krishenmathur1000/Analog-DJ-Board/simulation/Deck A passive crossfader.asc

C1: cap; 0.1µ
C2: cap; 0.1µ
R1: res; {10k*(1-aA)}
R2: res; {10k*aA}
R3: res; {160 + 10k*bA}
R4: res; {10k*(1-aB)}
R5: res; {10k*aB}
R6: res; {160 + 10k*bB}
R7: res; {10k*x+1}
R8: res; {10k*(1-x)+1}
U1: UniversalOpAmp2
U2: UniversalOpAmp2
V1: voltage; 0; AC 1
V2: voltage; 12
V3: voltage; 12
V4: voltage; 0; AC 0
V5: voltage; 12
V6: voltage; 12
Named nets: 0, DECKA_VOL_OUT, DECKA_FILTER_OUT, DECKB_VOL_OUT, DECKB_FILTER_OUT, XFADE
.ac dec 100 20 20k
.param aA=0.5
.param aB=0.5
.param bA=0
.param bB=0
.step param x list 0 0.25 0.5 0.75 1
