krishenmathur1000/Analog-DJ-Board/simulation/Deck A passive.asc

C1: cap; 0.1µ
R1: res; {10k*(1-a)}
R2: res; {10k*a}
R3: res; {160 + 10k*b}
V1: voltage; 0; AC 1
Named nets: 0, VOL_OUT, FILTER_OUT
.ac dec 100 20 20k
.param a=0.5
.param b=1
.step param b list 0.1 0.25 0.5 0.75 1
