krishenmathur1000/Analog-DJ-Board/results/crossfader_step_response.png

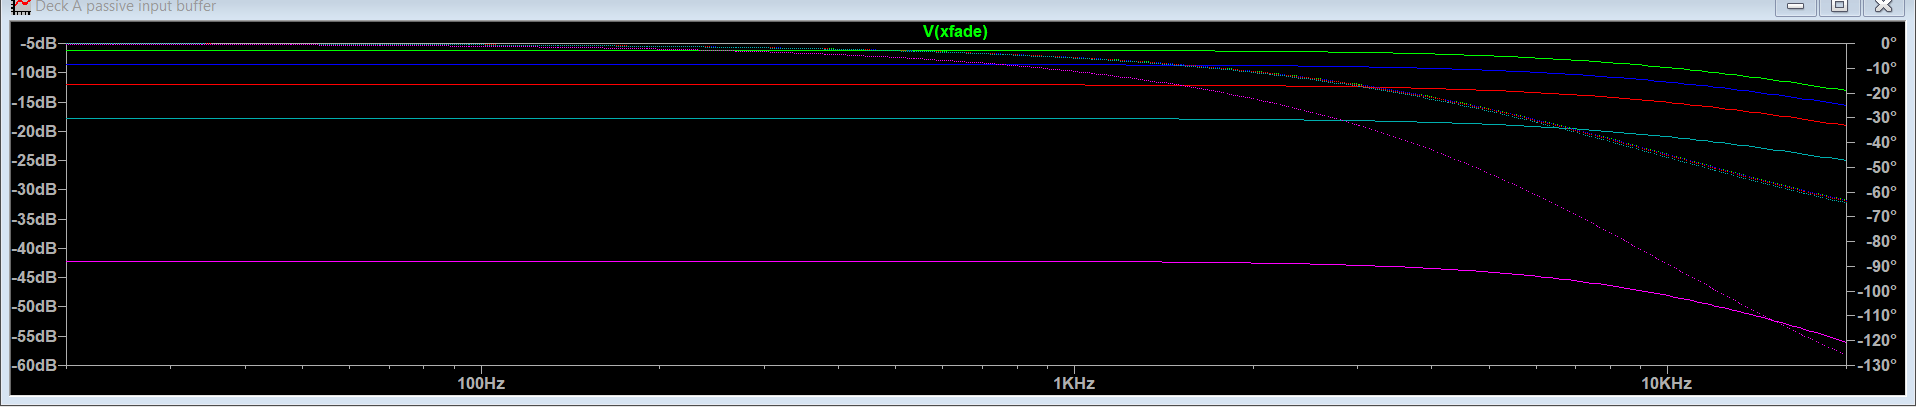
results/crossfader_step_response.png
