krishenmathur1000/Analog-DJ-Board/results/constant_power_plot.png

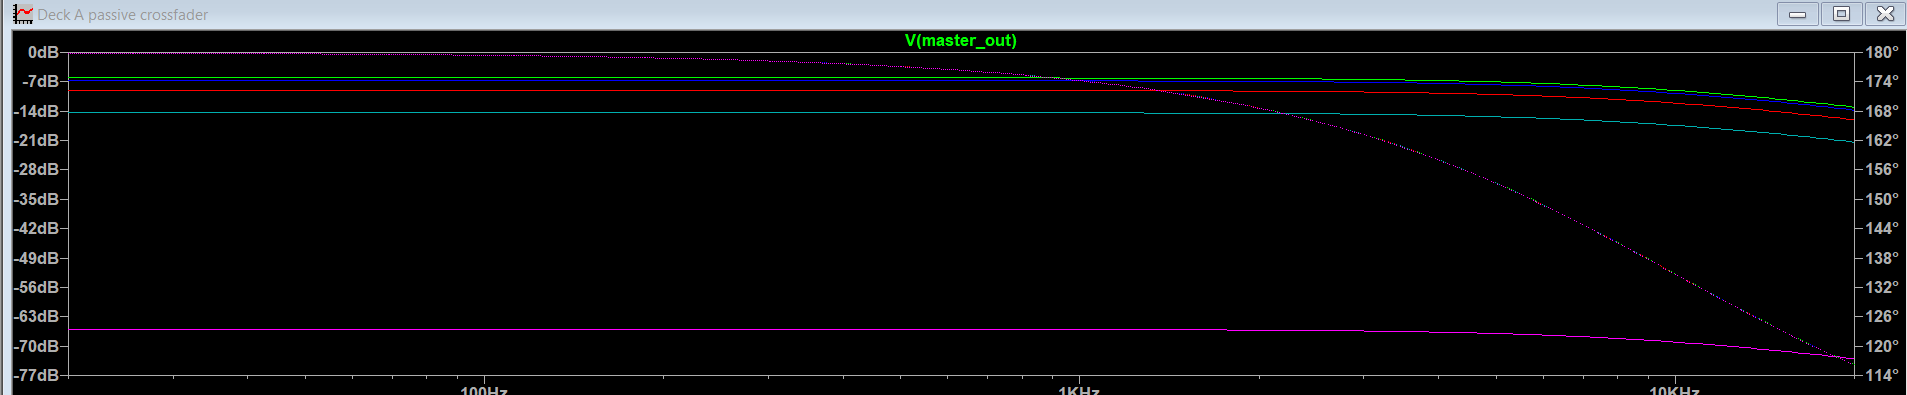
results/constant_power_plot.png
