krishenmathur1000/Analog-DJ-Board/results/Deck_A_passive.png

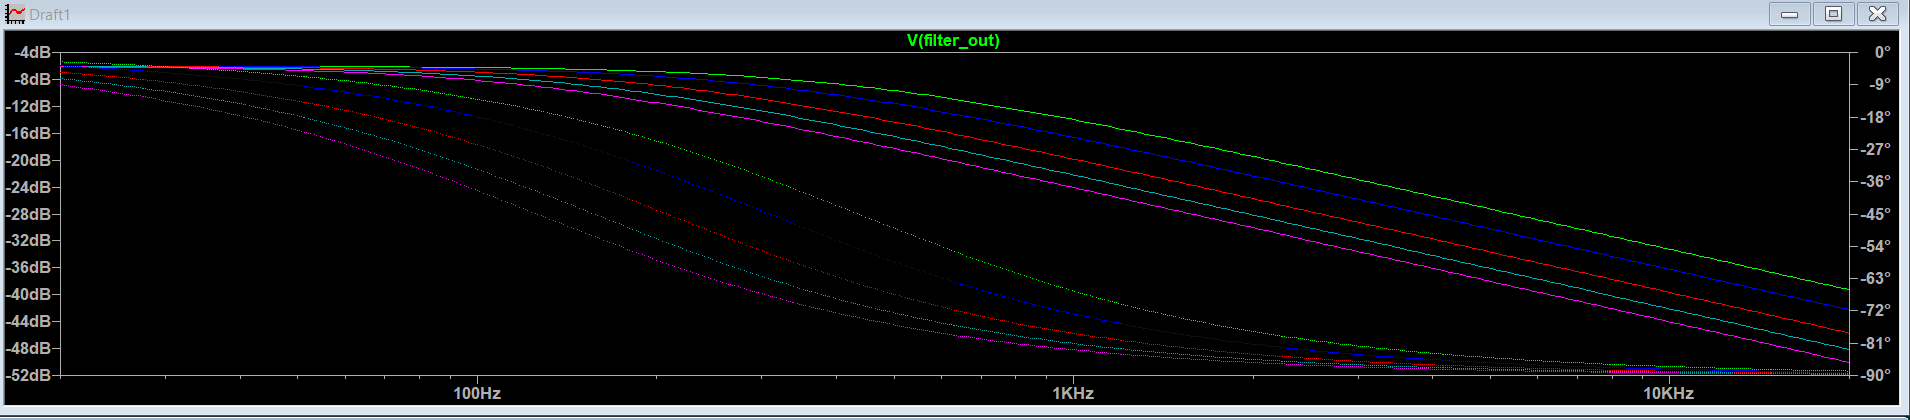
results/Deck_A_passive.png
