krishenmathur1000/Analog-DJ-Board/results/summing_amp.png

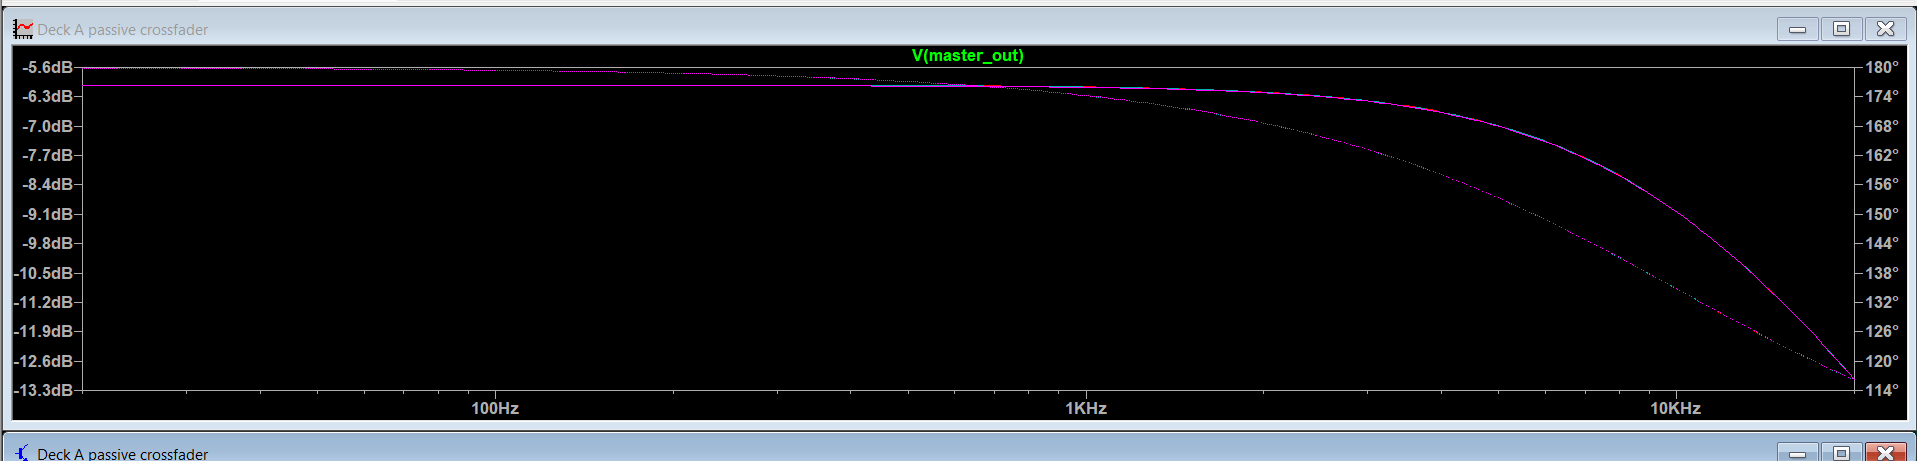
results/summing_amp.png
