krishenmathur1000/Analog-DJ-Board/results/weighted_crossfade_single_channel_sweep.png

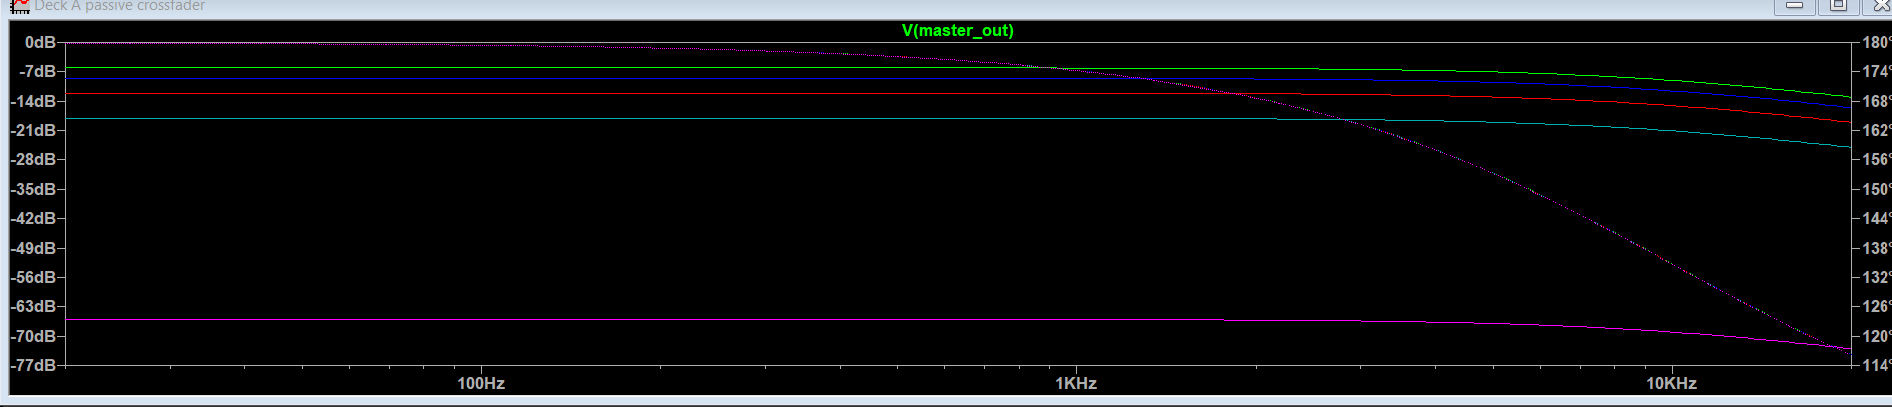
results/weighted_crossfade_single_channel_sweep.png
